jankae/Signalgenerator/Data/1g1.png

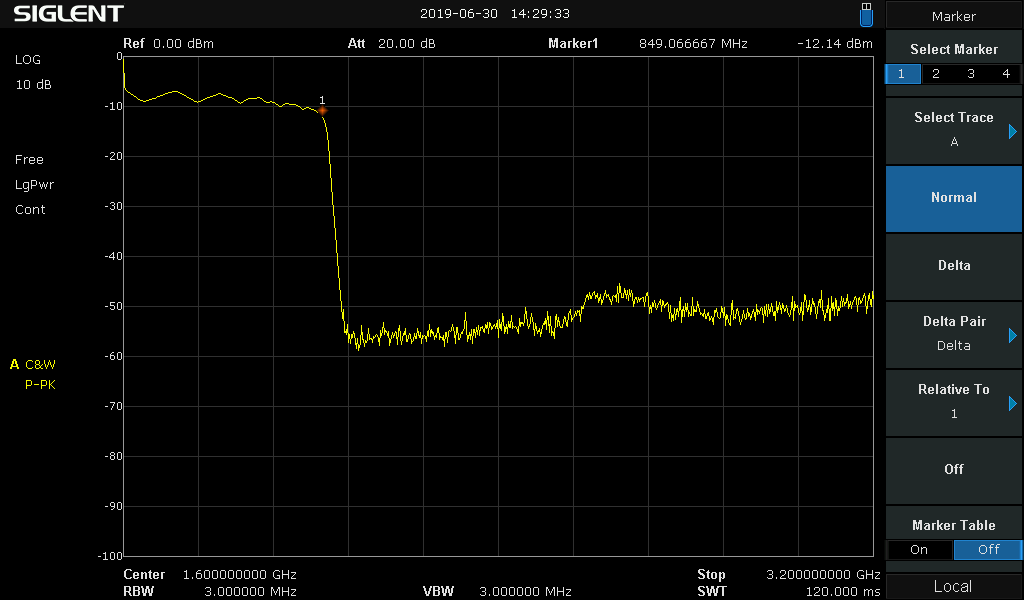
Data/1g1.png
