jankae/Signalgenerator/Data/2g5.png

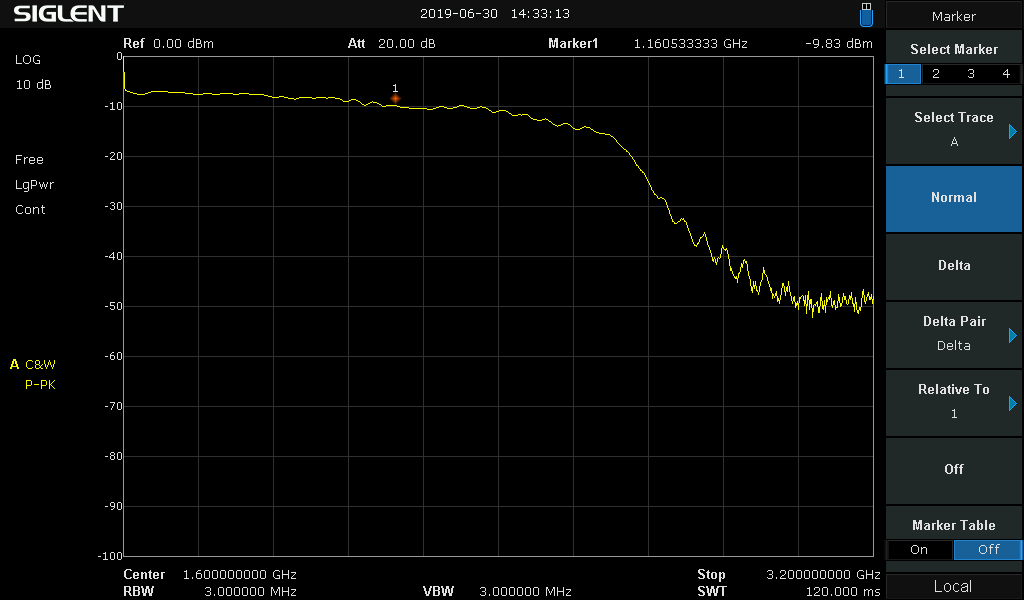
Data/2g5.png
