jankae/Signalgenerator/Data/340.png

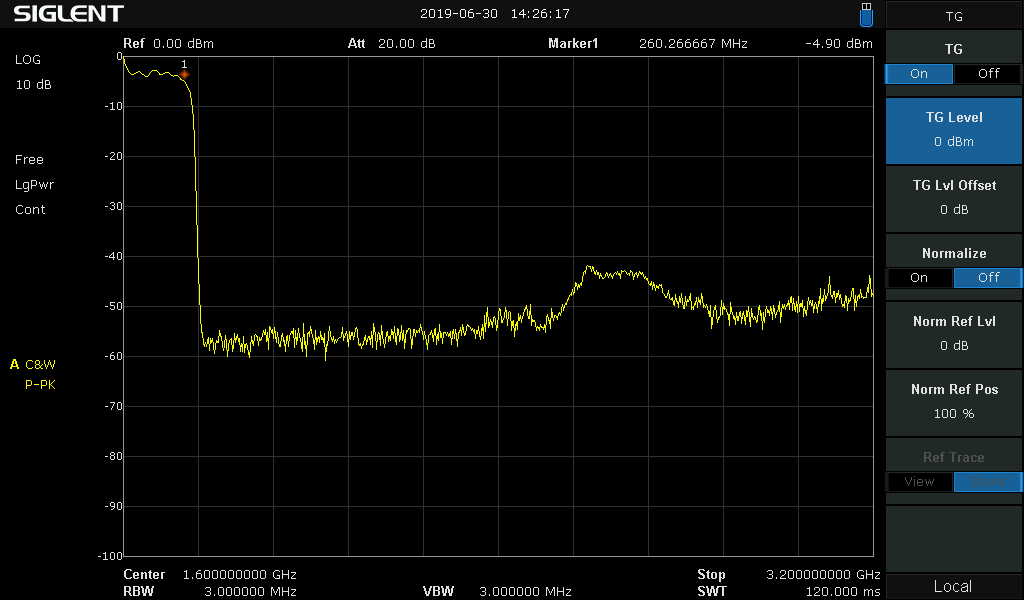
Data/340.png
