jankae/Signalgenerator/Data/500.png

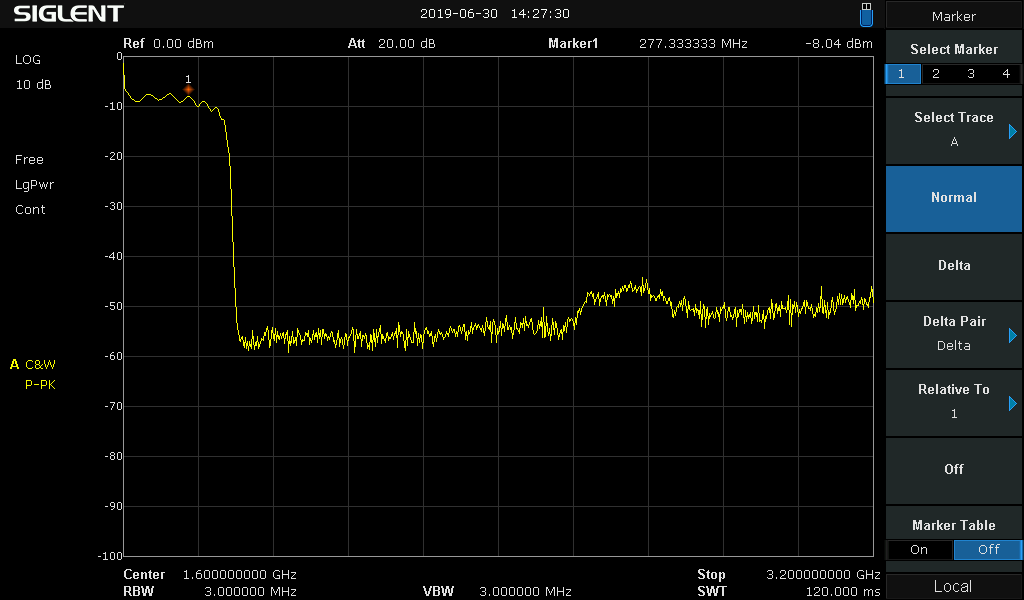
Data/500.png
