jankae/Signalgenerator/Data/mainpll.png

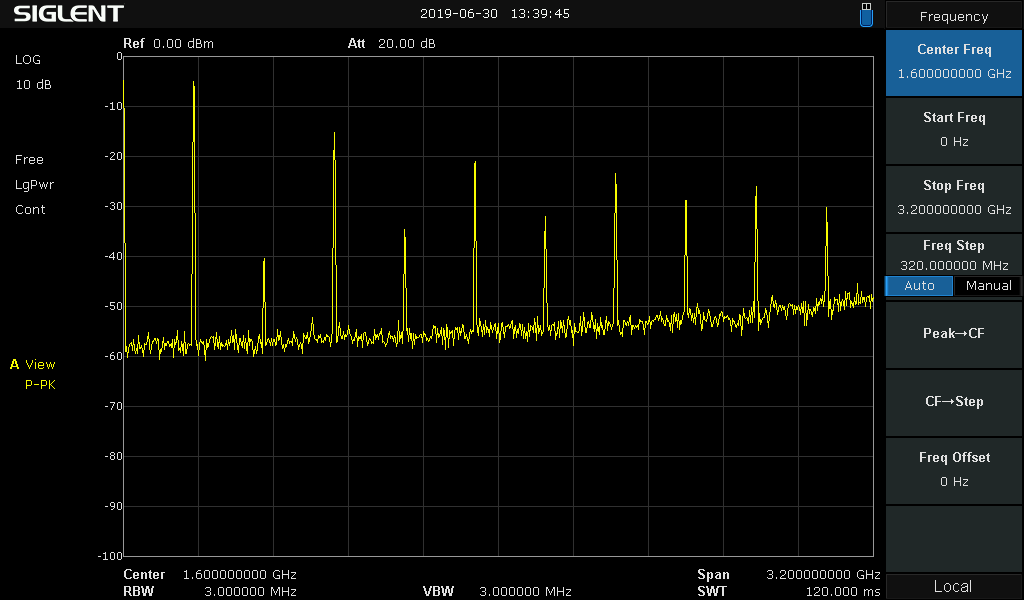
Data/mainpll.png
