jankae/Signalgenerator/Data/RFShield/After1.png

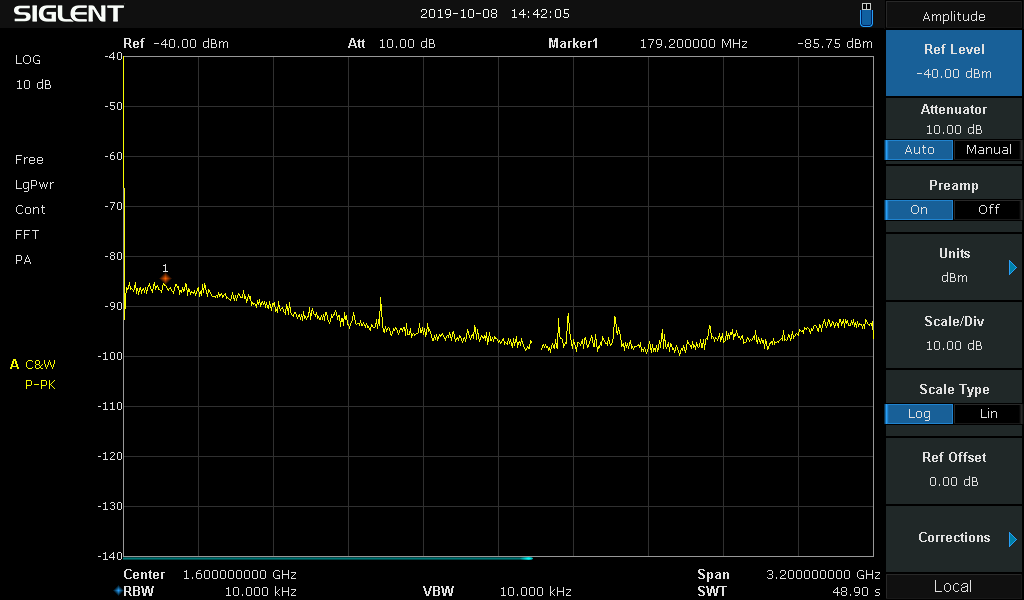
Data/RFShield/After1.png
