jankae/Signalgenerator/Hardware/Simulation/IQDDS.asc

B1: bi; I=(I(Rset)*16)*(1-I(IDAC))
B2: bi; I=(I(Rset)*16)*(1+I(IDAC))
C1: cap; 15p
C2: cap; 68p
C3: cap; 68p
C4: cap; 15p
C5: cap; 10µ
IDAC: current; SINE(0 0 1000)
L1: ind; 200n
L2: ind; 200n
L3: ind; 330n
L4: ind; 330n
L5: ind; 200n
L6: ind; 200n
R1: res; 50
R2: res; 50
R3: res; 1k
R4: res; 50
R5: res; 50
R6: res; 2k
R7: res; 2k
Rset: res; 2.2k
V1: voltage; 0
Vref: voltage; 1.2
Named nets: 0
.tran 10ms
