jankae/Signalgenerator/Hardware/Simulation/IQinput.asc

C1: cap; 68p
C2: cap; 18p
C3: cap; 0
C4: cap; 220p
C5: cap; 0
C6: cap; 0
C7: cap; 100p
C8: cap; 33p
C9: cap; 33p
R1: res; 1k
R2: res; 60k
R3: res; 190k
R4: res; 750k
R5: res; 1k
R6: res; 1k
R7: res; 470
R8: res; 470
R9: res; 470
R10: res; 470
R11: res; 49.9
R12: res; 49.9
U1: opamp2; OPA2810
U2: opamp2; OPA2810
U3: opamp2; OPA2810
U4: ad8132
V1: voltage; -2.8
V2: voltage; 3.3
V3: voltage; SINE(0 1 1000k); AC 1
V4: voltage; 0.9
Named nets: 0, VCC, VEE
.ac dec 20 1k 100000k
;tran 0.1ms
.include OPA2810.LIB
.include ad8132.lib
