jankae/Signalgenerator/Software/Signalgenerator/Abstraction/startup.cpp

#include <startup.h>

#include "adc.h"
#include "fatfs.h"
#include "file.hpp"
#include "input.h"

#include "display.h"
#include "buttons.h"
#include "Unit.hpp"
#include "Generator.hpp"
#include "Calibration.hpp"
#include "Persistence.hpp"
#include "SPIProtocol.hpp"

extern uint8_t pushpull_SPI_OK;

extern QueueHandle_t GUIeventQueue;

static uint8_t line;

typedef enum {TEST_PASSED = 0, TEST_FAILED = 1, TEST_WARNING = 2} TestResult_t;

/* Maximum allowed deviation of voltages in percent that still passes the test */
#define VOLTAGE_MAX_DEV		5
/* Tests whether exp and meas are the same value with some tolerance */
#define TEST_PERCENTDEV(exp, meas)	abs(((int32_t)(exp) - meas)*100/exp) <= VOLTAGE_MAX_DEV ? TEST_PASSED : TEST_FAILED
/* Tests a value for absolute limits */
#define TEST_ABSLIMITS(min, max, meas) (meas>=min && meas<=max) ? TEST_PASSED : TEST_FAILED

static uint16_t get_5VRail(void) {
	uint16_t result[2];
	HAL_ADC_Start_DMA(&hadc1, (uint32_t*) result, 2);
	/* wait for ADC to finish */
	HAL_Delay(10);
	/* convert to mV, full scale ADC is 6.6V */
	return (uint32_t) result[0] * 6600 / 4096;
}

static uint16_t get_3V3Rail(void) {
	uint16_t result[2];
	HAL_ADC_Start_DMA(&hadc1, (uint32_t*) result, 2);
	/* wait for ADC to finish */
	HAL_Delay(10);
	/* convert to mV, full scale ADC is 1.2V -> 1200mV * 4096 = 4915200 */
	return 4915200UL / result[1];
}

static bool CheckForRFBoard(uint32_t timeout) {
	extern SPI_HandleTypeDef hspi1;
	Protocol::FrontToRF send;
	Protocol::RFToFront recv;
	memset(&send, 0, sizeof(send));
	send.Status.UseIntRef = 1;

	uint32_t starttime = HAL_GetTick();
	do {
		HAL_Delay(100);
		SPI1_CS_RF_GPIO_Port->BSRR = SPI1_CS_RF_Pin << 16;
		HAL_SPI_TransmitReceive(&hspi1, (uint8_t*) &send, (uint8_t*) &recv,
				sizeof(send), 1000);
		SPI1_CS_RF_GPIO_Port->BSRR = SPI1_CS_RF_Pin;
		if (HAL_GetTick() - starttime > timeout) {
			// failed to establish communication in time
			return false;
		}
	} while (recv.MagicConstant != Protocol::MagicConstant);
	return true;
}

static bool CheckForIQInput(uint32_t timeout) {
	extern SPI_HandleTypeDef hspi1;
	Protocol::FrontToRF send;
	Protocol::RFToFront recv;
	memset(&send, 0, sizeof(send));
	send.Status.UseIntRef = 1;

	uint32_t starttime = HAL_GetTick();
	do {
		HAL_Delay(100);
		SPI1_CS_RF_GPIO_Port->BSRR = SPI1_CS_RF_Pin << 16;
		HAL_SPI_TransmitReceive(&hspi1, (uint8_t*) &send, (uint8_t*) &recv,
				sizeof(send), 1000);
		SPI1_CS_RF_GPIO_Port->BSRR = SPI1_CS_RF_Pin;
		if (HAL_GetTick() - starttime > timeout) {
			// failed to detect board in time
			return false;
		}
	} while (!recv.Status.IQADCAvailable);
	return true;
}

static void display_TestResult(const char * const name, const char * const result,
		TestResult_t res) {
	display_SetForeground(COLOR_WHITE);
	display_String(0, line * 16, name);
	if (res == TEST_PASSED) {
		display_SetForeground(COLOR_GREEN);
		printf("%s  %s PASSED\r\n", name, result);
	} else if (res == TEST_FAILED) {
		display_SetForeground(COLOR_RED);
		printf("%s %s FAILED\r\n", name, result);
	} else if (res == TEST_WARNING) {
		display_SetForeground(COLOR_YELLOW);
		printf("%s %s WARNING\r\n", name, result);
	}
	display_String(200, line * 16, result);
	line++;
}

static bool display_runLongerTest(const char *name,
		bool (*test_function)(void)) {
	// show indication that test is running
	display_SetForeground(COLOR_WHITE);
	display_String(0, line * 16, name);
	// run test
	bool success = test_function();
	if (success) {
		display_TestResult("", "OK", TEST_PASSED);
	} else {
		display_TestResult("", "FAILED", TEST_FAILED);
	}
	return success;
}

static void updateResult(TestResult_t *overall, TestResult_t res) {
	if(res == TEST_FAILED) {
		*overall = TEST_FAILED;
	} else if(res == TEST_WARNING) {
		*overall = TEST_WARNING;
	}
}

void startup_Hardware(void) {
	HAL_ADCEx_Calibration_Start(&hadc1);
	display_SetBackground(COLOR_BLACK);
	display_SetForeground(COLOR_WHITE);
	display_SetFont(Font_Big);
	display_Clear();
	display_String(0, 0, "Running selftest...");
	printf("Running selftest...\n");

	line = 1;

	char buffer[32];
	TestResult_t res;
	TestResult_t overallRes = TEST_PASSED;
	int32_t meas;

	/* Check frontpanel board voltages */
	meas = get_3V3Rail();
	res = TEST_PERCENTDEV(3300, meas);
	updateResult(&overallRes, res);
	Unit::StringFromValue(buffer, 6, meas * 1000, Unit::Voltage);
	display_TestResult("3.3V(1) rail:", buffer, res);

	meas = get_5VRail();
	res = TEST_PERCENTDEV(5000, meas);
	updateResult(&overallRes, res);
	Unit::StringFromValue(buffer, 6, meas * 1000, Unit::Voltage);
	display_TestResult("5V(1) rail:", buffer, res);

	if(overallRes != TEST_PASSED) {
		goto error;
	}

	/* Check connection to analog board */
//	if(pushpull_SPI_OK) {
//		display_TestResult("SPI Connection:", "OK", TEST_PASSED);
//	} else {
//		display_TestResult("SPI Connection:", "ERROR", TEST_FAILED);
//		goto error;
//	}

	if(overallRes != TEST_PASSED) {
		goto error;
	}

	if(overallRes != TEST_PASSED) {
error:
		display_SetForeground(COLOR_RED);
		display_String(0, 224, "HARDWARE ERROR. STOPPING.");
		// TODO Add key to continue anyway
		HAL_Delay(2000);
	} else {
		display_SetForeground(COLOR_GREEN);
		display_String(0, 224, "HARDWARE TESTS PASSED");
		HAL_Delay(500);
	}
}

void startup_Software(void) {
	display_SetBackground(COLOR_BLACK);
	display_SetForeground(COLOR_WHITE);
	display_SetFont(Font_Big);
	display_Clear();
	display_String(0, 0, "Booting...");

	Persistence::Init();

	line = 1;

	uint8_t error = 0;
	uint8_t warning = 0;

	/* Start sampling of frontpanel controls */
	buttons_Init();
    touch_Init();

 	Calibration::Init();

 	// No SD card handling for now
//	switch(File::Init()) {
//	case -1:
//		display_TestResult("SD card:", "INT ERR", TEST_FAILED);
//		error = 1;
//		break;
//	case 0:
//		display_TestResult("SD card:", "MISSING", TEST_WARNING);
//		warning = 1;
//		break;
//	case 1:
//		display_TestResult("SD card:", "OK", TEST_PASSED);
//		break;
//	}

	/* Initialize sampling of touch display */
	if(input_Init()==pdPASS) {
		display_TestResult("Touch thread:", "STARTED", TEST_PASSED);
	} else {
		display_TestResult("Touch thread:", "ERROR", TEST_FAILED);
		error = 1;
	}

	/* Load touch calibration */
	if(Persistence::Load()) {
		display_TestResult("Persistence:", "LOADED", TEST_PASSED);
	} else {
		display_TestResult("Persistence:", "CRC ERROR", TEST_WARNING);
		warning = 1;
	}

//	/* Setup Apps */

	/* Start GUI thread */
	if(gui_Init()) {
		display_TestResult("GUI thread:", "STARTED", TEST_PASSED);
	} else {
		display_TestResult("GUI thread:", "ERROR", TEST_FAILED);
		error = 1;
	}

	/* Check for RF board */
	if (!display_runLongerTest("RF board:", []() -> bool {
			return CheckForRFBoard(3000);
		})) {
		error = 1;
	} else {
		display_runLongerTest("IQ input board", []() -> bool {
			return CheckForIQInput(500);
		});
	}

	if (error) {
		display_SetForeground(COLOR_RED);
		display_String(0, 224, "SOFTWARE ERROR. STOPPING.");
		/* keep showing screen until there is some user input */
		GUIEvent_t event;
		while (xQueuePeek(GUIeventQueue, &event, 0) == pdFALSE) {
		}
	} else {
		display_SetForeground(COLOR_WHITE);
		display_String(0, 208, "Boot process completed.");
		char buffer[27];
		snprintf(buffer, sizeof(buffer), "Remaining HEAP: %lu",
				(uint32_t) xPortGetFreeHeapSize());
		display_String(0, 224, buffer);

		HAL_Delay(1000);
	}

	if (warning) {
		/* keep showing screen until there is some user input */
		GUIEvent_t event;
		while (xQueuePeek(GUIeventQueue, &event, 0) == pdFALSE) {
		}
	}

	Generator::Init();
}
