jankae/Signalgenerator/Software/RFControl/Application/app.cpp

#include "app.h"

#include "RF.hpp"
#include "SPIProtocol.hpp"
#include <string.h>
#include "stm32f0xx_hal.h"
#include "System/log.h"
#include "Drivers/fpga.hpp"
#include "Drivers/mcp48x2.hpp"
#include "main.h"

#define Log_App		(LevelAll)

static Protocol::RFToFront send;
static Protocol::FrontToRF spi_new, recv;

static volatile bool new_data = false;

extern SPI_HandleTypeDef hspi2;
extern SPI_HandleTypeDef hspi1;

static bool new_modulation_data = false;

static MCP48X2 OffsetDAC = MCP48X2(&hspi1, OFFSET_CS_GPIO_Port, OFFSET_CS_Pin);

static_assert(sizeof(Protocol::RFToFront) == 48);
static_assert(sizeof(Protocol::FrontToRF) == 48);

void app(void) {
//	RF::InternalReference(true);
	// keep FPGA in reset for now
	FPGA_RESET_GPIO_Port->BSRR = FPGA_RESET_Pin;

	log_init();
	RF::InternalReference(true);
	send.MagicConstant = Protocol::MagicConstant;

	OffsetDAC.Set(MCP48X2::Channel::A, MCP48X2::MaxValue / 2, false);
	OffsetDAC.Set(MCP48X2::Channel::B, MCP48X2::MaxValue / 2, false);

	Protocol::FrontToRF spi_current;
	memset(&spi_current, 0, sizeof(spi_current));
	// Wait for FPGA to finish loading configuration
	HAL_Delay(2000);
	// Release FPGA reset
	FPGA_RESET_GPIO_Port->BSRR = FPGA_RESET_Pin << 16;
	HAL_Delay(2);

	RF::Init(&send);

	HAL_SPI_TransmitReceive_DMA(&hspi2, (uint8_t*) &send, (uint8_t*) &recv,
			sizeof(spi_new));

	while (1) {
		while (!new_data)
			;
		new_data = false;
		HAL_SPI_TransmitReceive_DMA(&hspi2, (uint8_t*) &send, (uint8_t*) &recv,
					sizeof(spi_new));
		auto FPGA_status = FPGA::ReadStatus();
		send.Status.IQADCAvailable = FPGA_status.IQADCAvailable;
		send.Status.IADCOverload = FPGA_status.IADCOverload;
		send.Status.QADCOverload = FPGA_status.QADCOverload;

//		LOG(Log_System, LevelInfo,
//				"SPI data, freq: %lu, dbm: %u, intref: 0x%02x",
//				(uint32_t ) spi_new.frequency, spi_new.dbm,
//				(uint8_t ) spi_new.Status.UseIntRef);
		if (spi_new.frequency != spi_current.frequency
				|| spi_new.dbm != spi_current.dbm) {
			RF::Configure(spi_new.frequency, spi_new.dbm);
		}
		if (spi_new.Status.UseIntRef != spi_current.Status.UseIntRef) {
			RF::InternalReference(spi_new.Status.UseIntRef);
		}
		if (spi_new.Status.ADCCouplingDC != spi_current.Status.ADCCouplingDC
				|| spi_new.Status.ADCImp1M != spi_current.Status.ADCImp1M
				|| spi_new.Status.ADCRange1 != spi_current.Status.ADCRange1
				|| spi_new.Status.ADCRange2 != spi_current.Status.ADCRange2) {
			FPGA::ConfigureExtADC(spi_new.Status.ADCCouplingDC, spi_new.Status.ADCImp1M,
					spi_new.Status.ADCRange1, spi_new.Status.ADCRange2);
		}
		if (spi_new.offset_I != spi_current.offset_I) {
			uint16_t value = spi_new.offset_I / (UINT16_MAX / MCP48X2::MaxValue)
					+ MCP48X2::MaxValue / 2;
			OffsetDAC.Set(MCP48X2::Channel::A, value, false);
		}
		if (spi_new.offset_Q != spi_current.offset_Q) {
			uint16_t value = spi_new.offset_Q / (UINT16_MAX / MCP48X2::MaxValue)
					+ MCP48X2::MaxValue / 2;
			OffsetDAC.Set(MCP48X2::Channel::B, value, false);
		}
//		LOG(Log_System, LevelInfo,
//				"SPI data, Mod0: 0x%04x, Mod1: 0x%04x, Mod2: 0x%04x",
//				spi_new.modulation_registers[0],
//				spi_new.modulation_registers[1],
//				spi_new.modulation_registers[2]);
		if (!RF::Stabilized() || memcmp(spi_new.modulation_registers,
				spi_current.modulation_registers,
				sizeof(spi_new.modulation_registers))) {
			new_modulation_data = true;
			LOG(Log_App, LevelDebug, "Updating modulation registers required");
		}
		spi_current = spi_new;
		if (new_modulation_data && RF::Stabilized()) {
			// Update registers on FPGA
			for (uint8_t i = 0; i < 16; i++) {
				FPGA::WriteReg((FPGA::Reg) (i + (int) FPGA::Reg::MOD_REG0),
						spi_current.modulation_registers[i]);
			}
			new_modulation_data = false;
			LOG(Log_App, LevelDebug, "Updated modulation registers");
		}
	}
}

void HAL_SPI_TxRxCpltCallback(SPI_HandleTypeDef *hspi) {
	if (hspi == &hspi2) {
		// got new data from frontpanel
		spi_new = recv;
		new_data = true;
	}
}
