jankae/Signalgenerator/Software/Signalgenerator/Applications/FIRTapOrder.hpp

#pragma once

#include <cstdint>

static constexpr uint16_t FIRTapOrder[36] = {
		30,
		31,
		32,
		33,
		34,
		35,
		24,
		25,
		26,
		27,
		28,
		29,
		18,
		19,
		20,
		21,
		22,
		23,
		12,
		13,
		14,
		15,
		16,
		17,
		6,
		7,
		8,
		9,
		10,
		11,
		0,
		1,
		2,
		3,
		4,
		5
};
