jankae/Signalgenerator/Software/Signalgenerator/Abstraction/input.hpp

#ifndef INPUT_H_
#define INPUT_H_

#include <cstdint>
#include "events.hpp"

namespace Input {

constexpr uint32_t LongTouchTime = 1500;

bool Init();
void Calibrate();
bool LoadCalibration();
}


#endif
