jankae/Signalgenerator/Software/RFControl/Application/System/log.h

#ifndef LOG_H_
#define LOG_H_

#ifdef __cplusplus
extern "C" {
#endif

#include <stdint.h>

#define LOG_USART			1
#define LOG_SENDBUF_LENGTH	1024
/*
 * If the log message does not fit into the remaining buffer space it is
 * discarded to not block program flow. For debugging purposes this behaviour
 * might be irritating. In this case uncomment the following line. Whenever the
 * buffer is too full, a call to log_write blocks until enough space is available.
 */
#define LOG_BLOCKING

/*
 * Enables receive functionality for the Log USART. If defined, the function log_set_receive_handler
 * is available.
 */
//#define LOG_RECEIVE

#define USE_ASSERT

// log levels
#define LevelDebug 0x01
#define LevelInfo  0x02
#define LevelWarn  0x04
#define LevelError 0x08
#define LevelCrit  0x10
#define LevelAll   0x1F

// enabled levels for individual log sources
#define Log_System  	(LevelAll)

// if LevelDebug is omitted from this mask,
// debug message will not be logged regardless
// of individual source settings
#define Global_Level_Mask (LevelAll)

#define LOG(source, level, message, ...) do { \
    if (source & level & Global_Level_Mask) { \
       log_write(#source, level, message, ##__VA_ARGS__); \
    } \
} while (0)

#ifdef USE_ASSERT
#define ASSERT(x) do { \
	if(!(x)) { \
		log_write("    ASSERT", LevelCrit, "Assertion failed: %s, line %d", __FILE__, __LINE__); \
		log_flush(); \
		__BKPT(); \
	} \
} while (0)
#else
#define ASSERT(x)
#endif


void log_init();
void log_write(const char *module, uint8_t level, const char *fmt, ...);
void log_flush();
#ifdef LOG_RECEIVE
typedef void(*rec_cb)(uint8_t *data, uint16_t len);
void log_set_receive_handler(rec_cb handler, uint8_t *rec_buf, uint16_t buf_len);
#endif

void log_force(const char *fmt, ...);

#ifdef __cplusplus
}
#endif

#endif
