jankae/Signalgenerator/Software/Signalgenerator/Applications/Calibration.cpp

#include "Calibration.hpp"

#include "common.hpp"
#include "gui.hpp"
#include "SPIProtocol.hpp"
#include "Persistence.hpp"
#include "FPGA.hpp"
#include "Constellation.hpp"

extern SPI_HandleTypeDef hspi1;

static constexpr int16_t ideal_low = -4000;
static constexpr int16_t ideal_high = 0;
using AmplitudePoint = struct {
	uint32_t freq;
	int16_t low;
	int16_t high;
};

using BalancePoint = struct {
	uint32_t freq;
	int16_t I;
	int16_t Q;
};

using SkewPoint = struct {
	uint32_t freq;
	int16_t skew;
};

static constexpr uint8_t maxPoints = 10;
static AmplitudePoint AmplitudePoints[maxPoints];
static BalancePoint BalancePoints[maxPoints];
static SkewPoint SkewPoints[maxPoints];

static constexpr AmplitudePoint defaultAmplitudeCalibration[maxPoints] = {
		{10000000, ideal_low, 0},
		{100000000, ideal_low, 0},
		{200000000, ideal_low, 0},
		{500000000, ideal_low, 0},
		{750000000, ideal_low, 0},
		{1000000000, ideal_low, 0},
		{1250000000, ideal_low, 0},
		{1500000000, ideal_low, 0},
		{1750000000, ideal_low, 0},
		{2000000000, ideal_low, 0},
};

#define CAL_ZERO_BALANCE	-4832
#define CAL_MAX_NEG_BALANCE 10500

static constexpr BalancePoint defaultBalanceCalibration[maxPoints] = {
		{10000000, CAL_ZERO_BALANCE, CAL_ZERO_BALANCE},
		{249999999, CAL_ZERO_BALANCE, CAL_ZERO_BALANCE},
		{250000000, CAL_ZERO_BALANCE, CAL_ZERO_BALANCE},
		{500000000, CAL_ZERO_BALANCE, CAL_ZERO_BALANCE},
		{750000000, CAL_ZERO_BALANCE, CAL_ZERO_BALANCE},
		{1000000000, CAL_ZERO_BALANCE, CAL_ZERO_BALANCE},
		{1250000000, CAL_ZERO_BALANCE, CAL_ZERO_BALANCE},
		{1500000000, CAL_ZERO_BALANCE, CAL_ZERO_BALANCE},
		{1750000000, CAL_ZERO_BALANCE, CAL_ZERO_BALANCE},
		{2000000000, CAL_ZERO_BALANCE, CAL_ZERO_BALANCE},
};

static constexpr SkewPoint defaultSkewCalibration[maxPoints] = {
		{10000000, 0},
		{249999999, 0},
		{250000000, 0},
		{500000000, 0},
		{750000000, 0},
		{1000000000, 0},
		{1250000000, 0},
		{1500000000,  0},
		{1750000000, 0},
		{2000000000, 0},
};

void Calibration::Init() {
	DefaultAmplitude();
	DefaultBalance();
	DefaultSkew();
	Persistence::Add(AmplitudePoints, sizeof(AmplitudePoints));
	Persistence::Add(BalancePoints, sizeof(BalancePoints));
	Persistence::Add(SkewPoints, sizeof(SkewPoints));
}

void Calibration::DefaultAmplitude() {
	memcpy(AmplitudePoints, defaultAmplitudeCalibration, sizeof(AmplitudePoints));
}

void Calibration::RunAmplitude() {
	uint8_t step = 1;
	uint8_t new_step = 0;
	bool done = false;

	Window *w = new Window("dbm Calibration", Font_Big, COORDS(250, 150));
	Container *c = new Container(w->getAvailableArea());
	Label *lStep = new Label(20, Font_Big, Label::Orientation::CENTER);
	Label *lUsage = new Label("Turn knob until output matches", Font_Medium);
	Label *lValue = new Label(20, Font_Big, Label::Orientation::CENTER, COLOR_RED);
	Button *bPrev = new Button("Prev", Font_Big, [](void *ptr, Widget *w) {
		uint8_t *new_step = (uint8_t*) ptr;
		(*new_step)--;
	}, &new_step, COORDS(80, 40));
	Button *bNext = new Button("Next", Font_Big, [](void *ptr, Widget *w) {
		uint8_t *new_step = (uint8_t*) ptr;
		(*new_step)++;
	}, &new_step, COORDS(80, 40));
	Button *bSave = new Button("Save", Font_Big, [](void *ptr, Widget *w) {
		bool *done = (bool*) ptr;
		*done = true;
	}, &done, COORDS(80, 40));

	c->attach(lStep, COORDS(4, 5));
	c->attach(lUsage, COORDS(34, 25));
	c->attach(lValue, COORDS(4, 40));

	c->attach(bPrev, COORDS(2, c->getSize().y - bPrev->getSize().y - 2));
	c->attach(bNext,
			COORDS((c->getSize().x - bNext->getSize().x) / 2,
					c->getSize().y - bNext->getSize().y - 2));
	c->attach(bSave,
			COORDS(c->getSize().x - bSave->getSize().x - 2,
					c->getSize().y - bSave->getSize().y - 2));

	EventCatcher *e = new EventCatcher(c, [](GUIEvent_t *const ev) -> bool {
		// only capture encoder movements
		if(ev->type == EVENT_ENCODER_MOVED) {
			return true;
		} else {
			return false;
		}
	}, [](void *ptr, Widget *source, GUIEvent_t *ev){
		uint8_t *step = (uint8_t*) ptr;
		uint8_t pointIndex = *step / 2;
		int16_t *valueToChange = *step & 0x01 ? &AmplitudePoints[pointIndex].high : &AmplitudePoints[pointIndex].low;
		*valueToChange += ev->movement;
	}, &step);

	w->setMainWidget(e);
	bNext->select();

	constexpr uint8_t last_step = maxPoints * 2 - 1;

	while(!done) {
		if (new_step != step) {
			step = new_step;
			uint8_t pointIndex = step / 2;
			int16_t dbmval = step & 0x01 ? ideal_high : ideal_low;

			// update button states
			if (step == 0) {
				bPrev->setSelectable(false);
			} else {
				bPrev->setSelectable(true);
			}
			if (step >= last_step) {
				bNext->setSelectable(false);
			} else {
				bNext->setSelectable(true);
			}
			// update label text
			char buf[21];
			snprintf(buf, sizeof(buf), "Step %d/%d", step + 1, last_step + 1);
			lStep->setText(buf);
			char freq[10];
			char dbm[10];
			Unit::StringFromValue(freq, 8, AmplitudePoints[pointIndex].freq,
					Unit::Frequency);
			Unit::StringFromValue(dbm, 8, dbmval, Unit::dbm);
			snprintf(buf, sizeof(buf), "%s, %s", freq, dbm);
			lValue->setText(buf);
		}
		// send current setting to RFboard
		Protocol::FrontToRF send;
		Protocol::RFToFront recv;
		memset(&send, 0, sizeof(send));
		memset(&recv, 0, sizeof(recv));
		send.Status.UseIntRef = 1;
		uint8_t pointIndex = step / 2;
		int16_t dbmval =
				step & 0x01 ? AmplitudePoints[pointIndex].high : AmplitudePoints[pointIndex].low;

		send.frequency = AmplitudePoints[pointIndex].freq;
		send.dbm = dbmval;
		SPI1_CS_RF_GPIO_Port->BSRR = SPI1_CS_RF_Pin << 16;
		HAL_SPI_TransmitReceive(&hspi1, (uint8_t*) &send, (uint8_t*) &recv,
				sizeof(send), 1000);
		SPI1_CS_RF_GPIO_Port->BSRR = SPI1_CS_RF_Pin;
		vTaskDelay(100);
	}
	delete w;
	if(!Persistence::Save()) {
		Dialog::MessageBox("ERROR", Font_Big, "Failed to save\ndbm calibration",
				Dialog::MsgBox::OK, nullptr, false);
	}
}

int16_t Calibration::CorrectAmplitude(uint32_t freq, int16_t dbm) {
	uint8_t i = 0;
	for (; i < maxPoints; i++) {
		if (freq <= AmplitudePoints[i].freq) {
			break;
		}
	}
	int16_t low, high;
	if (i == 0) {
		low = AmplitudePoints[0].low;
		high = AmplitudePoints[0].high;
	} else {
		// interpolate between AmplitudePoints
		low = common_Map(freq, AmplitudePoints[i - 1].freq, AmplitudePoints[i].freq,
				AmplitudePoints[i - 1].low, AmplitudePoints[i].low);
		high = common_Map(freq, AmplitudePoints[i - 1].freq, AmplitudePoints[i].freq,
				AmplitudePoints[i - 1].high, AmplitudePoints[i].high);
	}
	// interpolate amplitude
	return common_Map(dbm, ideal_low, ideal_high, low, high);
}

void Calibration::DefaultBalance() {
	memcpy(BalancePoints, defaultBalanceCalibration, sizeof(BalancePoints));
}

void Calibration::RunBalance() {
	uint8_t step = 1;
	uint8_t new_step = 0;
	bool done = false;

	int32_t offset;

	Window *w = new Window("Offset Calibration", Font_Big, COORDS(250, 150));
	Container *c = new Container(w->getAvailableArea());
	Label *lStep = new Label(20, Font_Big, Label::Orientation::CENTER);
	Label *lUsage = new Label("Adjust knob to suppress carrier", Font_Medium);
	Label *lValue = new Label(20, Font_Big, Label::Orientation::CENTER, COLOR_RED);
	Entry<int32_t> *eValue = new Entry<int32_t>(&offset, nullptr, nullptr,
			Font_Big, 8, Unit::Voltage);
	eValue->setSelectable(false);
	Button *bPrev = new Button("Prev", Font_Big, [](void *ptr, Widget *w) {
		uint8_t *new_step = (uint8_t*) ptr;
		(*new_step)--;
	}, &new_step, COORDS(80, 35));
	Button *bNext = new Button("Next", Font_Big, [](void *ptr, Widget *w) {
		uint8_t *new_step = (uint8_t*) ptr;
		(*new_step)++;
	}, &new_step, COORDS(80, 35));
	Button *bSave = new Button("Save", Font_Big, [](void *ptr, Widget *w) {
		bool *done = (bool*) ptr;
		*done = true;
	}, &done, COORDS(80, 35));

	c->attach(lStep, COORDS(4, 5));
	c->attach(lUsage, COORDS(34, 25));
	c->attach(lValue, COORDS(4, 40));
	c->attach(eValue, COORDS(30, 60));

	c->attach(bPrev, COORDS(2, c->getSize().y - bPrev->getSize().y - 2));
	c->attach(bNext,
			COORDS((c->getSize().x - bNext->getSize().x) / 2,
					c->getSize().y - bNext->getSize().y - 2));
	c->attach(bSave,
			COORDS(c->getSize().x - bSave->getSize().x - 2,
					c->getSize().y - bSave->getSize().y - 2));

	EventCatcher *e = new EventCatcher(c, [](GUIEvent_t *const ev) -> bool {
		// only capture encoder movements
		if(ev->type == EVENT_ENCODER_MOVED) {
			return true;
		} else {
			return false;
		}
	}, [](void *ptr, Widget *source, GUIEvent_t *ev){
		uint8_t *step = (uint8_t*) ptr;
		uint8_t pointIndex = *step / 2;
		int16_t *valueToChange = *step & 0x01 ? &BalancePoints[pointIndex].Q : &BalancePoints[pointIndex].I;
		*valueToChange += ev->movement * 16;
	}, &step);

	w->setMainWidget(e);
	bNext->select();

	constexpr uint8_t last_step = maxPoints * 2 - 1;

	Constellation dummyConst;
	dummyConst.SetUsedPoints(2);
	FPGA::SetConstellation(dummyConst);
	FPGA::SetFIRRaisedCosine(8, 0.35f);

	while(!done) {
		if (new_step != step) {
			step = new_step;
			uint8_t pointIndex = step / 2;

			// update button states
			if (step == 0) {
				bPrev->setSelectable(false);
			} else {
				bPrev->setSelectable(true);
			}
			if (step >= last_step) {
				bNext->setSelectable(false);
			} else {
				bNext->setSelectable(true);
			}
			// update label text
			char buf[21];
			snprintf(buf, sizeof(buf), "Step %d/%d", step + 1, last_step + 1);
			lStep->setText(buf);
			char freq[10];
			Unit::StringFromValue(freq, 8, BalancePoints[pointIndex].freq,
					Unit::Frequency);
			char *offset = step & 0x01 ? "Q Offset" : "I Offset";
			snprintf(buf, sizeof(buf), "%s, %s", freq, offset);
			lValue->setText(buf);
		}

		uint8_t pointIndex = step / 2;
		int64_t value = step & 0x01 ? BalancePoints[pointIndex].Q : BalancePoints[pointIndex].I;
		value -= CAL_ZERO_BALANCE;
		offset = value * CAL_MAX_NEG_BALANCE / (INT16_MAX + CAL_ZERO_BALANCE);
		eValue->requestRedraw();
		// send current setting to RFboard
		Protocol::FrontToRF send;
		Protocol::RFToFront recv;
		memset(&send, 0, sizeof(send));
		memset(&recv, 0, sizeof(recv));
		send.Status.UseIntRef = 1;
		send.frequency = BalancePoints[pointIndex].freq;
		send.dbm = CorrectAmplitude(BalancePoints[pointIndex].freq, 0);

		send.offset_I = BalancePoints[pointIndex].I;
		send.offset_Q = BalancePoints[pointIndex].Q;
		// QAM modulation with both I and Q parts set to zero
		Protocol::Modulation mod;
		mod.type = Protocol::ModulationType::QAM2;
		mod.source = FPGA::ModSrc::Fixed;
		mod.Fixed.value = 0;
		mod.QAM.SamplesPerSymbol = 8;
		mod.QAM.SymbolsPerSecond = 1000;
		mod.QAM.differential = false;

		Protocol::SetupModulation(send, mod);

		SPI1_CS_RF_GPIO_Port->BSRR = SPI1_CS_RF_Pin << 16;
		HAL_SPI_TransmitReceive(&hspi1, (uint8_t*) &send, (uint8_t*) &recv,
				sizeof(send), 1000);
		SPI1_CS_RF_GPIO_Port->BSRR = SPI1_CS_RF_Pin;
		vTaskDelay(100);
	}
	delete w;
	if(!Persistence::Save()) {
		Dialog::MessageBox("ERROR", Font_Big, "Failed to save\balance calibration",
				Dialog::MsgBox::OK, nullptr, false);
	}
}

Calibration::IQOffset Calibration::CorrectBalance(uint32_t freq) {
	uint8_t i = 0;
	for (; i < maxPoints; i++) {
		if (freq <= BalancePoints[i].freq) {
			break;
		}
	}
	IQOffset ret;
	if (i == 0) {
		ret.I = BalancePoints[0].I;
		ret.Q = BalancePoints[0].Q;
	} else {
		// interpolate between AmplitudePoints
		ret.I = common_Map(freq, BalancePoints[i - 1].freq, BalancePoints[i].freq,
				BalancePoints[i - 1].I, BalancePoints[i].I);
		ret.Q = common_Map(freq, BalancePoints[i - 1].freq, BalancePoints[i].freq,
				BalancePoints[i - 1].Q, BalancePoints[i].Q);
	}

	return ret;
}

void Calibration::DefaultSkew() {
	memcpy(SkewPoints, defaultSkewCalibration, sizeof(SkewPoints));
}

void Calibration::RunSkew() {
	uint8_t step = 1;
	uint8_t new_step = 0;
	bool done = false;

	int32_t skew;

	Window *w = new Window("Skew Calibration", Font_Big, COORDS(250, 150));
	Container *c = new Container(w->getAvailableArea());
	Label *lStep = new Label(20, Font_Big, Label::Orientation::CENTER);
	Label *lUsage = new Label("Adjust knob to suppress sideband", Font_Medium);
	Label *lValue = new Label(20, Font_Big, Label::Orientation::CENTER, COLOR_RED);
	Entry<int32_t> *eValue = new Entry<int32_t>(&skew, nullptr, nullptr,
			Font_Big, 8, Unit::Degree);
	eValue->setSelectable(false);
	Button *bPrev = new Button("Prev", Font_Big, [](void *ptr, Widget *w) {
		uint8_t *new_step = (uint8_t*) ptr;
		(*new_step)--;
	}, &new_step, COORDS(80, 35));
	Button *bNext = new Button("Next", Font_Big, [](void *ptr, Widget *w) {
		uint8_t *new_step = (uint8_t*) ptr;
		(*new_step)++;
	}, &new_step, COORDS(80, 35));
	Button *bSave = new Button("Save", Font_Big, [](void *ptr, Widget *w) {
		bool *done = (bool*) ptr;
		*done = true;
	}, &done, COORDS(80, 35));

	c->attach(lStep, COORDS(4, 5));
	c->attach(lUsage, COORDS(34, 25));
	c->attach(lValue, COORDS(4, 40));
	c->attach(eValue, COORDS(30, 60));

	c->attach(bPrev, COORDS(2, c->getSize().y - bPrev->getSize().y - 2));
	c->attach(bNext,
			COORDS((c->getSize().x - bNext->getSize().x) / 2,
					c->getSize().y - bNext->getSize().y - 2));
	c->attach(bSave,
			COORDS(c->getSize().x - bSave->getSize().x - 2,
					c->getSize().y - bSave->getSize().y - 2));

	EventCatcher *e = new EventCatcher(c, [](GUIEvent_t *const ev) -> bool {
		// only capture encoder movements
		if(ev->type == EVENT_ENCODER_MOVED) {
			return true;
		} else {
			return false;
		}
	}, [](void *ptr, Widget *source, GUIEvent_t *ev){
		uint8_t *step = (uint8_t*) ptr;
		SkewPoints[*step].skew += ev->movement;
	}, &step);

	w->setMainWidget(e);
	bNext->select();

	constexpr uint8_t last_step = maxPoints - 1;

	while(!done) {
		if (new_step != step) {
			step = new_step;

			// update button states
			if (step == 0) {
				bPrev->setSelectable(false);
			} else {
				bPrev->setSelectable(true);
			}
			if (step >= last_step) {
				bNext->setSelectable(false);
			} else {
				bNext->setSelectable(true);
			}
			// update label text
			char buf[21];
			snprintf(buf, sizeof(buf), "Step %d/%d", step + 1, last_step + 1);
			lStep->setText(buf);
			char freq[10];
			Unit::StringFromValue(freq, 8, SkewPoints[step].freq,
					Unit::Frequency);
			snprintf(buf, sizeof(buf), "%s", freq);
			lValue->setText(buf);
		}

		skew = common_Map(SkewPoints[step].skew, 0, UINT16_MAX + 1, 0, 360000);
		eValue->requestRedraw();
		// send current setting to RFboard
		Protocol::FrontToRF send;
		Protocol::RFToFront recv;
		memset(&send, 0, sizeof(send));
		memset(&recv, 0, sizeof(recv));
		send.Status.UseIntRef = 1;
		send.frequency = SkewPoints[step].freq;
		send.dbm = CorrectAmplitude(SkewPoints[step].freq, 0);

		auto balance = Calibration::CorrectBalance(SkewPoints[step].freq);
		send.offset_I = balance.I;
		send.offset_Q = balance.Q;
		// QAM modulation with both I and Q parts set to zero
		Protocol::Modulation mod;
		mod.type = Protocol::ModulationType::FM_USB;
		mod.FM.deviation = 1000000;
		mod.FM.phase_offset = 49152 + SkewPoints[step].skew;
		mod.source = FPGA::ModSrc::Fixed;
		mod.Fixed.value = 4095;

		Protocol::SetupModulation(send, mod);

		SPI1_CS_RF_GPIO_Port->BSRR = SPI1_CS_RF_Pin << 16;
		HAL_SPI_TransmitReceive(&hspi1, (uint8_t*) &send, (uint8_t*) &recv,
				sizeof(send), 1000);
		SPI1_CS_RF_GPIO_Port->BSRR = SPI1_CS_RF_Pin;
		vTaskDelay(100);
	}
	delete w;
	if(!Persistence::Save()) {
		Dialog::MessageBox("ERROR", Font_Big, "Failed to save\balance calibration",
				Dialog::MsgBox::OK, nullptr, false);
	}
}

int16_t Calibration::CorrectSkew(uint32_t freq) {
	uint8_t i = 0;
	for (; i < maxPoints; i++) {
		if (freq <= SkewPoints[i].freq) {
			break;
		}
	}
	int16_t ret;
	if (i == 0) {
		ret = SkewPoints[0].skew;
	} else {
		// interpolate between AmplitudePoints
		ret = common_Map(freq, SkewPoints[i - 1].freq, SkewPoints[i].freq,
				SkewPoints[i - 1].skew, SkewPoints[i].skew);
	}

	return ret;
}

void Calibration::ResetPopup() {
	Window *w = new Window("Reset Calibration", Font_Big, SIZE(150, 180));
	auto c = new Container(w->getAvailableArea());

	bool resetAmplitude = false;
	auto cAmplitude = new Checkbox(&resetAmplitude, nullptr, SIZE(20,20));
	bool resetBalance = false;
	auto cBalance = new Checkbox(&resetBalance, nullptr, SIZE(20,20));
	bool resetSkew = false;
	auto cSkew = new Checkbox(&resetSkew, nullptr, SIZE(20,20));
	auto lAmplitude = new Label("Amplitude", Font_Big);
	auto lBalance = new Label("Balance", Font_Big);
	auto lSkew = new Label("Skew", Font_Big);

	c->attach(cAmplitude, COORDS(5, 5));
	c->attach(lAmplitude, COORDS(30, 7));
	c->attach(cBalance, COORDS(5, 35));
	c->attach(lBalance, COORDS(30, 37));
	c->attach(cSkew, COORDS(5, 65));
	c->attach(lSkew, COORDS(30, 67));

	bool abort = false, reset = false;

	auto callback_setTrue = [](void *ptr, Widget*) {
		bool *flag = (bool*) ptr;
		*flag = true;
	};

	Button *bAbort = new Button("Abort", Font_Big, callback_setTrue, &abort,
			COORDS(c->getSize().x / 2 - 10, 35));
	Button *bReset = new Button("Reset", Font_Big, callback_setTrue, &reset,
			COORDS(c->getSize().x / 2 - 10, 35));

	c->attach(bAbort, COORDS(2, c->getSize().y - bAbort->getSize().y - 2));
	c->attach(bReset,
			COORDS(c->getSize().x - bReset->getSize().x - 2,
					c->getSize().y - bReset->getSize().y - 2));

	w->setMainWidget(c);

	while(!abort && !reset) {
		vTaskDelay(100);
	}
	if (reset) {
		if (resetAmplitude) {
			DefaultAmplitude();
		}
		if (resetBalance) {
			DefaultBalance();
		}
		if (resetSkew) {
			DefaultSkew();
		}
		Persistence::Save();
	}
	delete w;
}
