jankae/Signalgenerator/Software/Signalgenerator/GUI/sevensegment.hpp

#ifndef GUI_SEVEN_H_
#define GUI_SEVEN_H_

#include <common.hpp>
#include <widget.hpp>
#include "display.h"
#include <limits>
//#include "font.h"
//#include "dialog.h"

template<typename T>
class SevenSegment : public Widget {
public:
	SevenSegment(T *value, uint8_t sLength, uint8_t sWidth, uint8_t length,
			uint8_t dot, color_t color, bool editable = false, T min =
					std::numeric_limits<T>::min(), T max =
					std::numeric_limits<T>::max()) {
		/* set member variables */
		this->value = value;
		segmentLength = sLength;
		segmentWidth = sWidth;
		this->length = length;
		this->dot = dot;
		this->color = color;
		this->selectable = editable;
		this->min = min;
		this->max = max;
		selectedDigit = 0;
		cb = nullptr;
		cbptr = nullptr;

		uint16_t height = sWidth + 2 * sLength + 6;
		uint16_t digitWidth = sWidth + sLength;
		size.y = height;
		size.x = digitWidth * length + sWidth * (length - 1) + 2;
	}

	void setCallback(Callback cb, void *ptr) {
		this->cb = cb;
		cbptr = ptr;
	}

private:
	void draw_Digit(int16_t x, int16_t y, uint8_t digit) {
		uint8_t i;
		for (i = 0; i < 7; i++) {
			/* Select color for this segment */
			if ((1 << i) & digitToSegments[digit]) {
				display_SetForeground(color);
			} else {
				display_SetForeground (Background);
			}

			/* draw the segment */
			int16_t offsetX = x + segmentStartX[i] * (segmentLength + 1);
			int16_t offsetY = y + segmentStartY[i] * (segmentLength + 1);

			if ((1 << i) & segmentOrientation) {
				/* this is a horizontal segment */
				display_HorizontalLine(offsetX + 1, offsetY, segmentLength);
				uint8_t j;
				for (j = 1; j <= segmentWidth / 2; j++) {
					display_HorizontalLine(offsetX + j + 1, offsetY + j,
							segmentLength - 2 * j);
					display_HorizontalLine(offsetX + j + 1, offsetY - j,
							segmentLength - 2 * j);
				}
			} else {
				/* this is a vertical segment */
				display_VerticalLine(offsetX, offsetY + 1, segmentLength);
				uint8_t j;
				for (j = 1; j <= segmentWidth / 2; j++) {
					display_VerticalLine(offsetX + j, offsetY + j + 1,
							segmentLength - 2 * j);
					display_VerticalLine(offsetX - j, offsetY + j + 1,
							segmentLength - 2 * j);
				}
			}
		}
	}

	void draw(coords_t offset) override {
		T buf = *value;
		uint8_t neg = 0;
		if (buf < 0) {
			buf = -buf;
			neg = 1;
		}
		uint8_t i;
		int16_t x = offset.x + (length - 1) * digitWidth() + segmentWidth / 2;
		int16_t y = offset.y + segmentWidth / 2;
		for (i = 0; i < length; i++) {
			if (i == length - 1) {
				/* this is the negative sign position */
				if (neg) {
					draw_Digit(x, y, 10);
				} else {
					draw_Digit(x, y, 11);
				}
			} else {
				draw_Digit(x, y, buf % 10);
				if (selected && i == selectedDigit) {
					display_SetForeground(COLOR_SELECTED);
				} else {
					display_SetForeground(COLOR_BG_DEFAULT);
				}
				display_RectangleFull(x - 1, y + 2 * segmentLength + 5,
						x + segmentLength + 2, y + 2 * segmentLength + 7);
			}
			if (dot && (dot == i + 1)) {
				/* draw dot in front of current digit */
				int16_t offsetX = x - segmentWidth;
				int16_t offsetY = y + 2 * (segmentLength + 1)
						- segmentWidth / 2;
				display_SetForeground(color);
				display_VerticalLine(offsetX, offsetY + 1, segmentWidth + 1);
				uint8_t j;
				for (j = 1; j <= segmentWidth / 2 + 1; j++) {
					display_VerticalLine(offsetX + j, offsetY + j + 1,
							segmentWidth - 2 * j + 1);
					display_VerticalLine(offsetX - j, offsetY + j + 1,
							segmentWidth - 2 * j + 1);
				}
			}
			x -= digitWidth();
			buf /= 10;
		}
	}
	void input(GUIEvent_t *ev) override {
		if (!selectable) {
			return;
		}
		switch (ev->type) {
		case EVENT_TOUCH_PRESSED: {
			int16_t x = size.x - ev->pos.x - segmentWidth / 2;
			selectedDigit = x / digitWidth();
			requestRedraw();
			ev->type = EVENT_NONE;
		}
			break;
		case EVENT_BUTTON_CLICKED:
			if ((ev->button & BUTTON_LEFT) && selectedDigit < length - 2) {
				selectedDigit++;
				requestRedraw();
				ev->type = EVENT_NONE;
			} else if ((ev->button & BUTTON_RIGHT) && selectedDigit > 0) {
				selectedDigit--;
				requestRedraw();
				ev->type = EVENT_NONE;
			} else if (ev->button & BUTTON_UP) {
				changeDigit(1);
				ev->type = EVENT_NONE;
			} else if (ev->button & BUTTON_DOWN) {
				changeDigit(-1);
				ev->type = EVENT_NONE;
			}
			break;
		case EVENT_ENCODER_MOVED:
			changeDigit(ev->movement);
			ev->type = EVENT_NONE;
			break;
		default:
			break;
		}
		return;
	}

	void changeDigit(int32_t increments) {
		int32_t inc = 1;
		for (uint8_t i = 0; i < selectedDigit; i++) {
			inc *= 10;
		}
		T newVal = *value + inc * increments;
		if (newVal > max) {
			newVal = max;
		} else if (newVal < min) {
			newVal = min;
		}
		*value = newVal;
		if(cb) {
			cb(cbptr, this);
		}
		requestRedraw();
	}

	uint8_t digitWidth() {
		return segmentLength + 2 * segmentWidth;
	}
	uint8_t digitHeight() {
		return 2 * segmentLength + segmentWidth;
	}

	Widget::Type getType() override { return Widget::Type::Sevensegment; };

	static constexpr color_t Background = COLOR_BG_DEFAULT;
	/* Index			Symbol
	 * 0-9				0-9
	 * 10				Negative-sign
	 * 11				Blank
	 */
	static constexpr inline uint8_t digitToSegments[12] = {
			0b00111111,
			0b00000110,
			0b01011011,
			0b01001111,
			0b01100110,
			0b01101101,
			0b01111101,
			0b00000111,
			0b01111111,
			0b01101111,
			0b01000000,
			0b00000000,
	};
	/* 0 = vertical, 1 = horizontal */
	static constexpr inline uint8_t segmentOrientation = 0b01001001;
	static constexpr inline uint8_t segmentStartX[7] = {
			0, 1, 1, 0, 0, 0, 0
	};
	static constexpr inline uint8_t segmentStartY[7] = {
			0, 0, 1, 2, 1, 0, 1
	};

    T *value;
    T min, max;
	Callback cb;
	void *cbptr;
    uint8_t selectedDigit;
    uint8_t segmentLength;
    uint8_t segmentWidth;
    uint8_t length;
    uint8_t dot;
    color_t color;
};



#endif
