jankae/Signalgenerator/Software/Signalgenerator/GUI/entry.hpp

#ifndef GUI_ENTRY_H_
#define GUI_ENTRY_H_

#include "widget.hpp"
#include "display.h"
#include "font.h"

#include "Dialog/ValueInput.hpp"
#include "Unit.hpp"

template<typename T>
class Entry : public Widget {
public:
	using Callback = void (*)(void *, Widget*);
	Entry(T *value, const T *max, const T *min, font_t font,
			uint8_t length, const Unit::unit *unit[], const color_t c = COLOR_FG_DEFAULT) {
		/* set member variables */
		this->value = value;
		limitPtr = true;
		this->maxptr = max;
		this->minptr = min;
		this->font = font;
		this->unit = unit;
		this->length = length;
	    cb = nullptr;
	    cbptr = nullptr;
	    editing = false;
	    dotSet = false;
	    editPos = 0;
		size.y = font.height + 3;
		size.x = font.width * length + 3;
		inputString = new char[length + 1];
		color = c;
	}
	Entry(T *value, T max, T min, font_t font,
			uint8_t length, const Unit::unit *unit[], const color_t c = COLOR_FG_DEFAULT) {
		/* set member variables */
		this->value = value;
		limitPtr = false;
		this->max = max;
		this->min = min;
		this->font = font;
		this->unit = unit;
		this->length = length;
	    cb = nullptr;
	    cbptr = nullptr;
	    editing = false;
	    dotSet = false;
	    editPos = 0;
		size.y = font.height + 3;
		size.x = font.width * length + 3;
		inputString = new char[length + 1];
		color = c;
	}
	~Entry() {
		if(inputString) {
			delete inputString;
		}
	}

	void setCallback(Callback cb, void *ptr) {
		this->cb = cb;
		cbptr = ptr;
	}
	void ChangeValue(T *value, const T *max, const T *min,
			const Unit::unit *unit[]) {
		this->value = value;
		this->max = max;
		this->min = min;
		this->unit = unit;
		requestRedraw();
	}

private:
	T constrainValue(T val) {
		T high = max;
		T low = min;
		if (limitPtr) {
			high = maxptr ? *maxptr : INT32_MAX;
			low = minptr ? *minptr : INT32_MIN;
		}
		if (val > high) {
			return high;
		} else if (val < low) {
			return low;
		}
		return val;
	}
	T InputStringValue(uint32_t multiplier) {
	    T value = 0;
	    uint8_t i;
	    uint32_t div = 0;
	    for (i = 0; i < length; i++) {
	        if (inputString[i] >= '0' && inputString[i] <= '9') {
	            value *= 10;
	            value += inputString[i] - '0';
	            if (div) {
	                div *= 10;
	            }
	        } else if (inputString[i] == '.') {
	            div = 1;
	        }
	    }
	    value *= multiplier;
	    if (div) {
	        value /= div;
	    }
		if (inputString[0] == '-') {
			value = -value;
		}
	    return value;
	}
	void ValueInputCallback(bool updated) {
		if(updated) {
			*value = constrainValue(*value);
			if(cb) {
				cb(cbptr, this);
			}
		}
	}

	void draw(coords_t offset) override {
	    /* calculate corners */
	    coords_t upperLeft = offset;
		coords_t lowerRight = upperLeft;
		lowerRight.x += size.x - 1;
		lowerRight.y += size.y - 1;
	//	if (selected) {
	//		display_SetForeground(COLOR_SELECTED);
	//	} else {
			display_SetForeground(Border);
	//	}
		display_Rectangle(upperLeft.x, upperLeft.y, lowerRight.x, lowerRight.y);

		/* display string */
		if (!editing) {
			/* construct value string */
			Unit::StringFromValue(inputString, length, *value, unit);
			if (selectable) {
				display_SetForeground(color);
			} else {
				display_SetForeground(COLOR_GRAY);
			}
		} else {
			display_SetForeground(COLOR_SELECTED);
		}
		if (selectable) {
			display_SetBackground(Background);
		} else {
			display_SetBackground(COLOR_UNSELECTABLE);
		}
		display_SetFont(font);
		display_String(upperLeft.x + 1, upperLeft.y + 2, inputString);
	}
	void input(GUIEvent_t *ev) override {
		if (!selectable) {
			return;
		}
	    switch(ev->type) {
	    case EVENT_TOUCH_RELEASED:
			new ValueInput<T>("New value?", value, unit,
					pmf_cast<void (*)(void*, bool), Entry,
							&Entry::ValueInputCallback>::cfn, this);
			ev->type = EVENT_NONE;
	    	break;
	    default:
	    	break;
	    }
	    return;
	}

	Widget::Type getType() override { return Widget::Type::Entry; };

	static constexpr color_t Background = COLOR_BG_DEFAULT;
	static constexpr color_t Border = COLOR_FG_DEFAULT;

    T *value;
	bool limitPtr;
    union {
		const T *maxptr;
		T max;
	};
	union {
    	const T *minptr;
		T min;
	};
    font_t font;
    const Unit::unit **unit;
    uint8_t length;
    color_t color;
	bool editing;
	bool dotSet;
	Callback cb;
	void *cbptr;
	uint8_t editPos;
    char *inputString;
};

#endif
