jankae/Signalgenerator/Software/Signalgenerator/GUI/progressbar.hpp

#ifndef PROGRESSBAR_HPP_
#define PROGRESSBAR_HPP_

#include <common.hpp>
#include <widget.hpp>
#include "display.h"

class ProgressBar : public Widget {
public:
	ProgressBar(coords_t size);

	void setState(uint8_t state);
private:
	void draw(coords_t offset) override;

	Widget::Type getType() override { return Widget::Type::Progressbar; };

	static constexpr color_t Border = COLOR_BLACK;
	static constexpr color_t Bar = COLOR_GREEN;
	static constexpr color_t Background = COLOR_BG_DEFAULT;

    uint8_t state;
};

#endif
